fachat/csa_cbmio/petio/Shell.vhd

----------------------------------------------------------------------------------
-- Company: 
-- Engineer: 
-- 
-- Create Date:    22:18:53 01/30/2026 
-- Design Name: 
-- Module Name:    Shell - Behavioral 
-- Project Name: 
-- Target Devices: 
-- Tool versions: 
-- Description: 
--
-- Dependencies: 
--
-- Revision: 
-- Revision 0.01 - File Created
-- Additional Comments: 
--
----------------------------------------------------------------------------------
library IEEE;
use IEEE.STD_LOGIC_1164.ALL;
use IEEE.STD_LOGIC_unsigned.ALL;
use ieee.numeric_std.all;

-- Uncomment the following library declaration if using
-- arithmetic functions with Signed or Unsigned values
--use IEEE.NUMERIC_STD.ALL;

-- Uncomment the following library declaration if instantiating
-- any Xilinx primitives in this code.
library UNISIM;
use UNISIM.VComponents.all;

entity Shell is
	Port (
		phi2: in std_logic;
		rwb: in std_logic;
		niosel: in std_logic;
		nres: in std_logic;
		A: in std_logic_vector(11 downto 0);
		D: inout std_logic_vector(7 downto 0);
				
		irq: out std_logic;
		nbe: out std_logic;
		
		-- Test fixture toggle
		-- used in test bench only, so defaults to off
		test_enable: in std_logic := '0';
		
		-- SPI (5V)
		spiiosel: out std_logic;
		spimosi: out std_logic;
		spimiso: in std_logic;
		spiclk: out std_logic;
		
		-- "left" rs232
		lcts: in std_logic;
		lrts: out std_logic;
		lrx: in std_logic;
		ltx: out std_logic;
		ldsr: in std_logic;
		ldtr: out std_logic;
		ldcd: in std_logic;
		lri: in std_logic;
		
		-- "right" rs232
		rcts: in std_logic;
		rrts: out std_logic;
		rrx: in std_logic;
		rtx: out std_logic;
		rdsr: in std_logic;
		rdtr: out std_logic;
		--rdcd: in std_logic;
		--rri: in std_logic;
		
		-- cassette interface
		c1sw: inout std_logic;
		cwr: inout std_logic;
		c1rd: in std_logic;
		c1mtr: out std_logic;
		
		-- userport
		up: inout std_logic_vector(13 downto 0);
		
		-- serial IEC
		datain: in std_logic;
		clkin: in std_logic;
		satnin: in std_logic;
		srqin: in std_logic;
		dataout: out std_logic;
		clkout: out std_logic;
		satnout: out std_logic;
		srqout: out std_logic;
		
		-- keyboard
		ksel: out std_logic_vector(3 downto 0);
		kin: in std_logic_vector(7 downto 0);
		
		-- IEEE488
		dio: inout std_logic_vector(7 downto 0);
		ren: inout std_logic;
		ifc: inout std_logic;
		ndac: inout std_logic;
		nrfd: inout std_logic;
		dav: inout std_logic;
		eoi: inout std_logic;
		atn: inout std_logic;
		psrq: inout std_logic;
		te: out std_logic;
		dc: out std_logic
	);
end Shell;

architecture Behavioral of Shell is

	signal D_in: std_logic_vector(7 downto 0);
	signal D_out: std_logic_vector(7 downto 0);
		
	signal nbe_out: std_logic;
	signal res: std_logic;
	signal phi2_int: std_logic;
	signal phi2_clk: std_logic;
	signal phi2_ibuf: std_logic;
	
	signal int_out: std_logic;
	signal qclk: std_logic;
	signal qclk_locked: std_logic;
	signal clk200_raw: std_logic;
	signal clk200: std_logic;
	signal clk200_locked: std_logic;
	signal clk200_status: std_logic_vector(1 downto 0);
	signal phi2x8: std_logic;
	signal phi2falling_en: std_logic;
	signal phi2rising_en: std_logic;
	signal uart_nres: std_logic;

	-- IEEE488 signals output from PET (depends on direction)
	signal ieee_is_out: std_logic;	-- 1 when sending from host (us) to device (on bus)
	signal ndac_out: std_logic;
	signal nrfd_out: std_logic;
	signal dav_out: std_logic;
	signal atn_out: std_logic;
	signal srq_out: std_logic;
	signal eoi_out: std_logic;
	signal dio_out: std_logic_vector(7 downto 0);

	-- Serial IEC
	signal fserdir: std_logic;
	
	-- components and related signals
	
	component ioselect is
    Port ( A : in  STD_LOGIC_VECTOR (11 downto 0);
           niosel : in  STD_LOGIC;
			  iopage : in STD_LOGIC;
			  nres : in STD_LOGIC;
			  nbe : out std_logic;
           pia1 : out  STD_LOGIC;
           pia2 : out  STD_LOGIC;
           via1 : out  STD_LOGIC;
           via2 : out  STD_LOGIC;
           uart1 : out  STD_LOGIC;
           uart2 : out  STD_LOGIC);	
	end component;

	signal pia1_sel: std_logic;
	signal pia1_irq: std_logic;
	signal pia1_din: std_logic_vector(7 downto 0);
	signal pia1_dout: std_logic_vector(7 downto 0);
	signal pia1_pa_in: std_logic_vector(7 downto 0);
	signal pia1_pa_dir: std_logic_vector(7 downto 0);
	signal pia1_pa_out: std_logic_vector(7 downto 0);
	signal pia1_ca1_in: std_logic;
	signal pia1_ca2_in: std_logic;
	signal pia1_ca2_out: std_logic;
	signal pia1_pb_in: std_logic_vector(7 downto 0);
	signal pia1_pb_dir: std_logic_vector(7 downto 0);
	signal pia1_pb_out: std_logic_vector(7 downto 0);
	signal pia1_cb1_in: std_logic;
	signal pia1_cb2_in: std_logic;
	signal pia1_cb2_out: std_logic;

	signal pia2_sel: std_logic;
	signal pia2_irq: std_logic;
	signal pia2_din: std_logic_vector(7 downto 0);
	signal pia2_dout: std_logic_vector(7 downto 0);
	signal pia2_pa_in: std_logic_vector(7 downto 0);
	signal pia2_pa_dir: std_logic_vector(7 downto 0);
	signal pia2_pa_out: std_logic_vector(7 downto 0);
	signal pia2_ca1_in: std_logic;
	signal pia2_ca2_in: std_logic;
	signal pia2_ca2_out: std_logic;
	signal pia2_pb_in: std_logic_vector(7 downto 0);
	signal pia2_pb_dir: std_logic_vector(7 downto 0);
	signal pia2_pb_out: std_logic_vector(7 downto 0);
	signal pia2_cb1_in: std_logic;
	signal pia2_cb2_in: std_logic;
	signal pia2_cb2_out: std_logic;

	signal via1_sel: std_logic;
	signal via1_irq: std_logic;
	signal via1_wren: std_logic;
	signal via1_rden: std_logic;
	signal via1_din: std_logic_vector(7 downto 0);
	signal via1_dout: std_logic_vector(7 downto 0);
	signal via1_pa_in: std_logic_vector(7 downto 0);
	signal via1_pa_out: std_logic_vector(7 downto 0);
	signal via1_pa_dir: std_logic_vector(7 downto 0);
	signal via1_ca1_in: std_logic;
	signal via1_ca2_in: std_logic;
	signal via1_ca2_out: std_logic;
	signal via1_ca2_dir: std_logic;
	signal via1_pb_in: std_logic_vector(7 downto 0);
	signal via1_pb_out: std_logic_vector(7 downto 0);
	signal via1_pb_dir: std_logic_vector(7 downto 0);
	signal via1_cb1_in: std_logic;
	signal via1_cb1_out: std_logic;
	signal via1_cb1_dir: std_logic;
	signal via1_cb2_in: std_logic;
	signal via1_cb2_out: std_logic;
	signal via1_cb2_dir: std_logic;

	signal via2_sel: std_logic;
	signal via2_irq: std_logic;
	signal via2_wren: std_logic;
	signal via2_rden: std_logic;
	signal via2_din: std_logic_vector(7 downto 0);
	signal via2_dout: std_logic_vector(7 downto 0);
	signal via2_pa_in: std_logic_vector(7 downto 0);
	signal via2_pa_out: std_logic_vector(7 downto 0);
	signal via2_pa_dir: std_logic_vector(7 downto 0);
	signal via2_ca1_in: std_logic;
	signal via2_ca2_in: std_logic;
	signal via2_ca2_out: std_logic;
	signal via2_ca2_dir: std_logic;
	signal via2_pb_in: std_logic_vector(7 downto 0);
	signal via2_pb_out: std_logic_vector(7 downto 0);
	signal via2_pb_dir: std_logic_vector(7 downto 0);
	signal via2_cb1_in: std_logic;
	signal via2_cb1_out: std_logic;
	signal via2_cb1_dir: std_logic;
	signal via2_cb2_in: std_logic;
	signal via2_cb2_out: std_logic;
	signal via2_cb2_dir: std_logic;
	
	signal uart1_sel: std_logic;
	signal uart1_irq: std_logic;
	signal uart1_din: std_logic_vector(7 downto 0);
	signal uart1_dout: std_logic_vector(7 downto 0);

	signal uart2_sel: std_logic;
	signal uart2_irq: std_logic;
	signal uart2_din: std_logic_vector(7 downto 0);
	signal uart2_dout: std_logic_vector(7 downto 0);
	
	component pia6520 is
    Port ( nres : in  STD_LOGIC;
           phi2 : in  STD_LOGIC;
           rwb : in  STD_LOGIC;
           sel : in  STD_LOGIC;
           irq : out  STD_LOGIC;
			  addr : in STD_LOGIC_VECTOR(1 downto 0);
           data_in : in  STD_LOGIC_VECTOR (7 downto 0);
           data_out : out  STD_LOGIC_VECTOR (7 downto 0);

           porta_in : in  STD_LOGIC_VECTOR (7 downto 0);
           porta_dir : out  STD_LOGIC_VECTOR (7 downto 0);
           porta_out : out  STD_LOGIC_VECTOR (7 downto 0);
           ca1_in : in  STD_LOGIC;
           ca2_in : in  STD_LOGIC;
           ca2_out : out  STD_LOGIC;
			  
           portb_in : in  STD_LOGIC_VECTOR (7 downto 0);
           portb_dir : out  STD_LOGIC_VECTOR (7 downto 0);
           portb_out : out  STD_LOGIC_VECTOR (7 downto 0);
           cb1_in : in  STD_LOGIC;
           cb2_in : in  STD_LOGIC;
           cb2_out : out  STD_LOGIC);
	end component;

	component via6522 is
		port (
			phi2        : in  std_logic;
			phi2x8      : in  std_logic;
			phi2falling_en : in  std_logic;
			phi2rising_en  : in  std_logic;
			reset       : in  std_logic;
    
			addr        : in  std_logic_vector(3 downto 0);
			wen         : in  std_logic;
			ren         : in  std_logic;
			data_in     : in  std_logic_vector(7 downto 0);
			data_out    : out std_logic_vector(7 downto 0);

--			phi2_ref    : out std_logic;

			-- pio --
			port_a_o    : out std_logic_vector(7 downto 0);
			port_a_t    : out std_logic_vector(7 downto 0);
			port_a_i    : in  std_logic_vector(7 downto 0);
    
			port_b_o    : out std_logic_vector(7 downto 0);
			port_b_t    : out std_logic_vector(7 downto 0);
			port_b_i    : in  std_logic_vector(7 downto 0);

			-- handshake pins
			ca1_i       : in  std_logic;

			ca2_o       : out std_logic;
			ca2_i       : in  std_logic;
			ca2_t       : out std_logic;
    
			cb1_o       : out std_logic;
			cb1_i       : in  std_logic;
			cb1_t       : out std_logic;
    
			cb2_o       : out std_logic;
			cb2_i       : in  std_logic;
			cb2_t       : out std_logic;

			irq         : out std_logic );
	end component;
	
	component ieeedir is
    Port ( 
           phi2 : in  STD_LOGIC;
           nres : in  STD_LOGIC;
			  dio_in : in  STD_LOGIC_VECTOR (7 downto 0);
           atn_in : in  STD_LOGIC;
           dav_in : in  STD_LOGIC;
           nrfd_in : in  STD_LOGIC;
			  is_out : out STD_LOGIC
	 );
	end component;

	component uart_shell is
    Port ( phi2 : in  STD_LOGIC;
           qclk : in  STD_LOGIC;
           rwb : in  STD_LOGIC;
           nres : in  STD_LOGIC;
			  sel : in STD_LOGIC;
           addr : in  STD_LOGIC_VECTOR (2 downto 0);
           din : in  STD_LOGIC_VECTOR (7 downto 0);
           dout : out  STD_LOGIC_VECTOR (7 downto 0);
           irq : out  STD_LOGIC;
           rx : in  STD_LOGIC;
           tx : out  STD_LOGIC;
           cts : in  STD_LOGIC;
           rts : out  STD_LOGIC;
           dsr : in  STD_LOGIC;
           dtr : out  STD_LOGIC;
           ri : in  STD_LOGIC;
           dcd : in  STD_LOGIC);
	end component;

	component qclk_pll is
    Port ( phi2 : in  STD_LOGIC;
           nres : in  STD_LOGIC;
           qclk : out  STD_LOGIC;
           phi2x8 : out  STD_LOGIC;
           phi2falling_en : out  STD_LOGIC;
           phi2rising_en : out  STD_LOGIC;
           locked : out  STD_LOGIC);
	end component;
	
	-- test timer (50Hz)
	signal test_counter: std_logic_vector(15 downto 0);
	-- test
	signal ign_rtx: std_logic;
	signal ign_rrts: std_logic;
	
	-- which I/O page to use (either 8 or 9)
	signal iopage: std_logic;
	
	-- divider for qclk
	signal qclk_cnt: std_logic_vector(7 downto 0);
	signal qclk_div: std_logic;

	attribute keep : string;
	attribute keep of clk200 : signal is "true";
	
begin

	-- phi2 is a CLK signal
	-- phi2_int isn't
	phi2_ibufg: IBUFG
		port map (
			I => phi2,
			O => phi2_ibuf
		);
	phi2_bufg: BUFG
		port map (
			I => phi2_ibuf,
			O => phi2_clk
		);

	clk200_gen: DCM_CLKGEN
		generic map (
			CLKFXDV_DIVIDE => 2,
			CLKFX_DIVIDE => 1,
			CLKFX_MD_MAX => 0.0,
			CLKFX_MULTIPLY => 200,
			CLKIN_PERIOD => 1000.0,
			SPREAD_SPECTRUM => "NONE",
			STARTUP_WAIT => FALSE
		)
		port map (
			CLKFX => clk200_raw,
			CLKFX180 => open,
			CLKFXDV => open,
			LOCKED => clk200_locked,
			PROGDONE => open,
			STATUS => clk200_status,
			CLKIN => phi2_clk,
			FREEZEDCM => '0',
			PROGCLK => '0',
			PROGDATA => '0',
			PROGEN => '0',
			RST => not nres
		);

	clk200_bufg: BUFG
		port map (
			I => clk200_raw,
			O => clk200
		);
	
	phi2_int <= phi2_ibuf;
	
--	phi2_int <= phi2;
--	phi2_clk <= phi2;
	
	rtx <= '1' when via1_sel ='1' and A(3 downto 0) = X"6" else '0';
	rrts <= qclk_div; --nbe_out; --D_in(2);
	iopage <= rcts;
	
	qclk_div_p: process(qclk, qclk_cnt, nres)
	begin
		if (nres = '0') then
--			qclk_cnt <= (others => '0');
		elsif (falling_edge(qclk)) then
				qclk_div <= not(qclk_div);
		end if;
	end process;
	
	
	irq <= pia1_irq 
		or pia2_irq 
		or via1_irq 
		or uart1_irq
		or uart2_irq
		or int_out;
	
	res <= not(nres);
	uart_nres <= nres and qclk_locked;
	
	D_in <= D;
	D <= (others => 'Z') when rwb = '0'
			else D_out;	
	D_out <= pia1_dout when pia1_sel = '1'
			else pia2_dout when pia2_sel = '1'
			else via1_dout when via1_sel = '1'
			else via2_dout when via2_sel = '1'
			else uart1_dout when uart1_sel = '1'
			else uart2_dout when uart2_sel = '1'
			else "11101000";	-- open bus pattern $e8
			--else (others => 'X');

	-- I/O
	
	-- userport (inputs)
	up(8) <= 'Z';
	up(12) <= 'Z' when via1_cb1_dir = '0' else via1_cb1_out;
	up(13) <= 'Z';

	-- SPI (5V)
	spimosi <= '1';
	spiclk <= '1';
	spiiosel <= '1';
	
	-- IEEE488
	
	-- Using the 7516x interface chips
	-- https://www.ti.com/lit/ds/symlink/sn75161b.pdf?ts=1774340006842
	--
	-- 75161 direction control; 0 = controller
	-- ATN out, SRQ in, REN out, IFC out
	dc <= '0';
	-- 7516x talk enable; 0: DAV in, EOI in (ATN hi), NRFD out, NDAC out
	-- 						 PET receives = TALK from device
	-- 7516x talk enable; 1: DAV out, EOI out, NRFD in, NDAC in
	-- 						 PET sends data = ATN, device LISTENs
	te <= ieee_is_out;
	
	atn <= atn_out;
	ren <= '1';
	ifc <= '1';
	psrq <= 'Z';

	ndac <= ndac_out when ieee_is_out = '0' else 'Z';
	nrfd <= nrfd_out when ieee_is_out = '0' else 'Z';
	dav <= dav_out when ieee_is_out = '1' else 'Z';
	eoi <= eoi_out when ieee_is_out = '1' else 'Z';
	
	dio(7 downto 0) <= dio_out when ieee_is_out = '1' else (others => 'Z');
	
	----------------------------------------------------
	-- fake interrupt as long as pia int does not seem to work
	
	fake_int: block
		signal int_cnt: std_logic_vector(15 downto 0);
	begin
	  int_p: process(phi2_int, nres)
	  begin
		if  (falling_edge(phi2_int)) then
			if (nres = '0') then
				int_cnt <= (others => '0');
			elsif (int_cnt > 20000) then
				int_cnt <= (others => '0');
			else
				int_cnt <= int_cnt + 1;
			end if;
		end if;
		if (rising_edge(phi2_int)) then
			if (int_cnt < 100) then
				int_out <= '1';
			else
				int_out <= '0';
			end if;
		end if;
	  end process;
	end block fake_int;
	
	----------------------------------------------------

	qclk_c: qclk_pll
		port map (
			phi2 => phi2_clk,
			nres => nres,
			qclk => qclk,
			phi2x8 => phi2x8,
			phi2falling_en => phi2falling_en,
			phi2rising_en => phi2rising_en,
			locked => qclk_locked
		);

	----------------------------------------------------

	pia1_c: pia6520
	   Port map (
			nres,
         phi2_int,
         rwb,
         pia1_sel,
         pia1_irq,
			A(1 downto 0),
         pia1_din,
			pia1_dout,

			pia1_pa_in,
			pia1_pa_dir,
			pia1_pa_out,			
         pia1_ca1_in,
         pia1_ca2_in,
         pia1_ca2_out,

			pia1_pb_in,
			pia1_pb_dir,
			pia1_pb_out,			
         pia1_cb1_in,
         pia1_cb2_in,
         pia1_cb2_out
		);

	pia1_din <= D_in;
	
	ksel <= pia1_pa_out(3 downto 0);
	pia1_pb_in <= kin;
	
	pia1_pa_in(7) <= up(10) when test_enable = '0' or via1_cb1_dir = '0' else via1_cb1_out;
	up(10) <= pia1_pa_out(7) when pia1_pa_dir(7) = '1' else 'Z';
	
	pia1_pa_in(6) <= eoi;
	pia1_pa_in(5) <= '1';	-- cass#2 switch
	pia1_pa_in(4) <= c1sw;	-- cass#1 switch
	pia1_pa_in(3 downto 0) <= pia1_pa_out(3 downto 0);

	c1sw <= pia1_pa_out(4) when pia1_pa_dir(0) = '1' else 'Z';
	
	-- cass#1 read
	pia1_ca1_in <= c1rd when test_enable = '0' or via1_ca2_dir = '0' else via1_ca2_out;
	-- eoi out
	pia1_ca2_in <= 'X';
	eoi_out <= pia1_ca2_out;
	
	pia1_cb1_in <= up(13);	-- vdrive
	pia1_cb2_in <= '1';	-- c1mtr out
	c1mtr <= pia1_cb2_out;
	
	----------------------------------------------------

	pia2_c: pia6520
	   Port map (
			nres,
         phi2_int,
         rwb,
         pia2_sel,
         pia2_irq,
			A(1 downto 0),
         pia2_din,
			pia2_dout,

			pia2_pa_in,
			pia2_pa_dir,
			pia2_pa_out,			
         pia2_ca1_in,
         pia2_ca2_in,
         pia2_ca2_out,

			pia2_pb_in,
			pia2_pa_dir,
			pia2_pb_out,			
         pia2_cb1_in,
         pia2_cb2_in,
         pia2_cb2_out
		);

	pia2_din <= D_in;
	
	pia2_pa_in <= dio;		-- dio out
	pia2_pb_in <= dio;
	dio_out <= pia2_pb_out;

	pia2_ca1_in <= atn;
	pia2_ca2_in <= 'X';		-- ndac out
	ndac_out <= pia2_ca2_out;
	
	pia2_cb1_in <= psrq;
	
	pia2_cb2_in <= 'X';		-- dav out
	dav_out <= pia2_cb2_out;
		
	----------------------------------------------------

	via1_c: via6522
	   Port map (
         phi2_clk,
			phi2x8,
			phi2falling_en,
			phi2rising_en,
			res,
			A(3 downto 0),
			via1_wren,
			via1_rden,			
         via1_din,
			via1_dout,

			via1_pa_out,			
			via1_pa_dir,			
			via1_pa_in,

			via1_pb_out,			
			via1_pb_dir,
			via1_pb_in,
			
         via1_ca1_in,
			
         via1_ca2_out,
         via1_ca2_in,
         via1_ca2_dir,

         via1_cb1_out,
         via1_cb1_in,
         via1_cb1_dir,

         via1_cb2_out,
         via1_cb2_in,
         via1_cb2_dir,
			
			via1_irq
		);
		
	via1_wren <= '1' when via1_sel = '1' and rwb = '0' else '0';
	via1_rden <= '1' when via1_sel = '1' and rwb = '1' else '0';
	
	via1_din <= D_in;

	via1_pa_in(0) <= up(0) when test_enable = '0' or via1_pa_dir(1) = '0' else via1_pa_out(1);
	via1_pa_in(1) <= up(1) when test_enable = '0' or via1_pa_dir(0) = '0' else via1_pa_out(0);
	via1_pa_in(2) <= up(2) when test_enable = '0' or via1_pa_dir(3) = '0' else via1_pa_out(3);
	via1_pa_in(3) <= up(3) when test_enable = '0' or via1_pa_dir(2) = '0' else via1_pa_out(2);
	via1_pa_in(4) <= up(7) when test_enable = '0' or via1_pb_dir(3) = '0' else via1_pb_out(3);
	via1_pa_in(5) <= up(6) when test_enable = '0' or via1_pa_dir(6) = '0' else via1_pa_out(6);
	via1_pa_in(6) <= up(5) when test_enable = '0' or via1_pa_dir(5) = '0' else via1_pa_out(5);
	via1_pa_in(7) <= up(4);
	
	via1_pb_in(0) <= ndac and ndac_out;
	via1_pb_in(1) <= 'Z'; -- nrfd out
	via1_pb_in(2) <= 'Z'; -- atn out
	via1_pb_in(3) <= cwr when test_enable = '0' or via1_pa_dir(4) = '0' else via1_pa_out(4);
	via1_pb_in(4) <= 'Z'; -- C2 MTR out
	
	up(0) <= via1_pa_out(0) when via1_pa_dir(0) = '1' else 'Z';
	up(1) <= via1_pa_out(1) when via1_pa_dir(1) = '1' else 'Z';
	up(2) <= via1_pa_out(2) when via1_pa_dir(2) = '1' else 'Z';
	up(3) <= via1_pa_out(3) when via1_pa_dir(3) = '1' else 'Z';
	up(4) <= via1_pa_out(7) when via1_pa_dir(7) = '1' else 'Z';
	up(5) <= via1_pa_out(6) when via1_pa_dir(6) = '1' else 'Z';
	up(6) <= via1_pa_out(5) when via1_pa_dir(5) = '1' else 'Z';
	up(7) <= via1_pa_out(4) when via1_pa_dir(4) = '1' else 'Z';
	
	nrfd_out <= via1_pb_out(1);
	atn_out <= via1_pb_out(2);
	cwr <= via1_pb_out(3) when via1_pb_dir(3) = '1' else 'Z';
	
	-- c2mtr <= via_pb_out(4);
	via1_pb_in(5) <= up(13);	-- vdrive
	via1_pb_in(6) <= nrfd and nrfd_out;
	via1_pb_in(7) <= dav;
	
	-- graphic
	up(11) <= via1_ca2_out when via1_ca2_dir = '1' else 'Z';
	via1_ca2_in <= up(11);
	
	-- Userport CA1
	via1_ca1_in <= up(8);
	-- Cass#2 read
	via1_cb1_in <= up(12) when test_enable = '0' or pia1_pa_dir(7) = '0' else pia1_pa_out(7);
	
	-- shift register in/out
	up(9) <= via1_cb2_out when via1_cb2_dir = '1' else 'Z';
	via1_cb2_in <= up(9) when test_enable = '0' or via1_pa_dir(7) = '0' else via1_pa_out(7);
	
	----------------------------------------------------

	via2_c: via6522
	   Port map (
         phi2_clk,
			phi2x8,
			phi2falling_en,
			phi2rising_en,
			res,
			A(3 downto 0),
			via2_wren,
			via2_rden,			
         via2_din,
			via2_dout,

			via2_pa_out,			
			via2_pa_dir,			
			via2_pa_in,

			via2_pb_out,			
			via2_pb_dir,
			via2_pb_in,
			
         via2_ca1_in,
			
         via2_ca2_out,
         via2_ca2_in,
         via2_ca2_dir,

         via2_cb1_out,
         via2_cb1_in,
         via2_cb1_dir,

         via2_cb2_out,
         via2_cb2_in,
         via2_cb2_dir,
			
			via2_irq
		);
		
	via2_ca1_in <= '1';
	via2_ca2_in <= '1';
	
	via2_wren <= '1' when via2_sel = '1' and rwb = '0' else '0';
	via2_rden <= '1' when via2_sel = '1' and rwb = '1' else '0';
	
	via2_din <= D_in;
	
	-- serial IEC bus
	-- TODO: satna, fast bus
	satnout 	<= via2_pb_out(3);
	clkout 	<= via2_pb_out(4);
	
	dataout 	<= via2_pb_out(5) or not(via2_cb2_out) when fserdir = '0' 
				else via2_pb_out(5);	
--	srqout <= not(via2_cb1_out) when fserdir = '0' 
--				else '0';
	srqout <= '0';
	
	fserdir <= via2_pb_out(0);
	
	via2_cb1_in <= srqin or not(fserdir);
	via2_cb2_in <= datain or not(fserdir);
	
	via2_pa_in <= (others => '1');
	
	via2_pb_in(0) <= '1'; -- fserdir
	via2_pb_in(1) <= '1'; -- satna
	via2_pb_in(2) <= not(satnin);	
	via2_pb_in(3) <= via2_pb_out(3);	-- atnout
	via2_pb_in(4) <= via2_pb_out(4);	-- clkout
	via2_pb_in(5) <= via2_pb_out(5);	-- dataout
	via2_pb_in(6) <= not(clkin);
	via2_pb_in(7) <= not(datain);

	----------------------------------------------------
	
--	uart1: uart_shell 
--    Port map ( 
--				phi2_int,
--				qclk,
--				rwb,
--				uart_nres,
--				uart1_sel,
--				A(2 downto 0),
--				uart1_din,
--				uart1_dout,
--				uart1_irq,
--				lrx,
--				ltx,
--				lcts,
--				lrts,
--				ldsr,
--				ldtr,
--				lri,
--				ldcd
--	);

	uart1_din <= D_in;

--	uart2: uart_shell 
--    Port map ( 
--				phi2_int,
--				qclk,
--				rwb,
--				uart_nres,
--				uart2_sel,
--				A(2 downto 0),
--				uart2_din,
--				uart2_dout,
--				uart2_irq,
--				rrx,
--				ign_rtx,
--				rcts,
--				ign_rrts,
--				rdsr,
--				rdtr,
--				'0',
--				'0'
--	);

	ltx <= '1';
	ldtr <= '1';
	rdtr <= '1';
	lrts <= '1';

	uart2_din <= D_in;
	
	----------------------------------------------------

	ieeedir_c: ieeedir
	port map(
		phi2_int,
		nres,
		not(dio),
		atn,
		dav,
		nrfd,
		ieee_is_out
	);
	
	-- IO select
	select_c: ioselect
	port map(
		A,
		niosel,
		iopage,
		nres,
		nbe_out,
		pia1_sel,
		pia2_sel,
		via1_sel,
		via2_sel,
		uart1_sel,
		uart2_sel
	);
	
	nbe <= nbe_out;
	
end Behavioral;
