fachat/csa_cbmio/petio/via6522_tmr_b.vhd

-------------------------------------------------------------------------------
-- Title      : VIA 6522 Timer B
-------------------------------------------------------------------------------

library ieee;
use ieee.std_logic_1164.all;
use ieee.std_logic_arith.all;
use ieee.std_logic_unsigned.all;

entity via6522_tmr_b is
port (
    phi2           : in  std_logic;
    phi2x8         : in  std_logic;
    phi2falling_en : in  std_logic;
    phi2rising_en  : in  std_logic;
    reset          : in  std_logic;
    acr            : in  std_logic_vector(7 downto 0);
    port_b_i       : in  std_logic_vector(7 downto 0);
    write_t2c_h    : in  std_logic;
    last_data      : in  std_logic_vector(7 downto 0);
    timer_b_latch  : in  std_logic_vector(7 downto 0);
    timer_b_count  : out std_logic_vector(15 downto 0);
    timer_b_event  : out std_logic;
    timer_b_sr_tick: out std_logic);
end via6522_tmr_b;

architecture rtl of via6522_tmr_b is
    constant latch_reset_pattern : std_logic_vector(15 downto 0) := X"5550";

    alias shift_mode_control : std_logic_vector(2 downto 0) is acr(4 downto 2);

    signal t2_count        : std_logic_vector(15 downto 0);
    signal t2_count_next   : std_logic_vector(15 downto 0);
    signal t2_count_prev   : std_logic_vector(15 downto 0);
    signal t2l_latch       : std_logic_vector(7 downto 0);
    signal w_t2c_h         : std_logic;
    signal t2_pb6_reg      : std_logic;
    signal t2_pb6_fall     : std_logic;
    signal t2l_ufl_prev    : std_logic;
    signal t2l_ufl_reg     : std_logic;
    signal t2h_ufl         : std_logic;
    signal t2l_load        : std_logic;
	 signal t2_cin				: std_logic;
    signal t2_run          : std_logic;
    signal s_t2            : std_logic;
    signal s_t2_prev       : std_logic;
begin

    timer_b_event <= s_t2;
    timer_b_count <= t2_count;
    t2l_latch <= timer_b_latch;
    timer_b_sr_tick <= t2l_ufl_reg;

    t2l_load <= '1' when (t2l_ufl_prev = '1' and (shift_mode_control = "100" or shift_mode_control(1 downto 0) = "01")) or w_t2c_h = '1' else '0';
    --t2_count_next <= (t2_count_prev - 1) when t2_cin = '1' else t2_count_prev;

    process(phi2x8)
        variable t2_pb6_sampled : std_logic;
    begin

		-- t2_pb6_reg is falling
		--> t2_pb6_fall is rising
		--> t2_pb6_sampled is rising
		if (rising_edge(phi2)) then
			if (reset = '1') then
				t2_pb6_fall <= '0';
			else
            t2_pb6_sampled := To_X01(port_b_i(6));
            if (t2_pb6_reg = '1' and t2_pb6_sampled = '0') then
					t2_pb6_fall <= '1';
            else
               t2_pb6_fall <= '0';
				end if;
         end if;
		end if;

		-- t2_pb6_sampled is rising
		--> t2_pb6_reg is falling
		if (falling_edge(phi2)) then
			if (reset = '1') then
				t2_pb6_reg <= '1';
			else
				t2_pb6_reg <= t2_pb6_sampled;
			end if;
      end if;

		-- write_t2c_h is incoming, valid at falling
		--> w_t2c_h is falling
		if (falling_edge(phi2)) then
			if (reset = '1') then
            w_t2c_h <= '0';
			else
            w_t2c_h <= write_t2c_h;
			end if;
		end if;

		-- w_t2c_h is falling
		-- t2l_latch is falling
		-- last_data is incoming, valid between falling
		-- t2_counter_next is t2_counter_prev is falling
		-- t2l_load is w_t2c_h, t2l_ufl_prev is falling
		--> t2_count is rising
		--> t2h_ufl is rising
		--> t2l_ufl_reg is rising
		if (rising_edge(phi2)) then
			if (reset = '1') then
				t2_count <= latch_reset_pattern;
            t2h_ufl <= '0';
            t2l_ufl_reg <= '0';
			else
                if (t2l_load = '1') then
                    t2_count(7 downto 0) <= t2l_latch;
                else
                    t2_count(7 downto 0) <= t2_count_next(7 downto 0);
                end if;

                if (w_t2c_h = '1') then
                    t2_count(15 downto 8) <= last_data;
                else
                    t2_count(15 downto 8) <= t2_count_next(15 downto 8);
                end if;

                if (t2_count_prev = x"0000" and t2_cin = '1' and w_t2c_h = '0') then
                    t2h_ufl <= '1';
                else
                    t2h_ufl <= '0';
                end if;
					 
                if t2_count_prev(7 downto 0) = x"00" and t2_cin = '1' and t2l_load = '0' then
                    t2l_ufl_reg <= '1';
                else
                    t2l_ufl_reg <= '0';
					 end if;
			end if;
		end if;

		-- t2_count is rising
		-- t2l_ufl_reg is rising
		--> t2_cin is falling
		--> t2_count_prev is falling
		--> t2l_ufl_prev is falling
		if (falling_edge(phi2)) then
			if (reset = '1') then
				t2_cin <= '0';
				t2_count_prev <= latch_reset_pattern;
				t2l_ufl_prev <= '0';
--				t2l_load <= '0';
			else
            if (acr(5) = '0' or t2_pb6_fall = '1') then
                t2_cin <= '1';
					 t2_count_next <= t2_count - 1;
            else
                t2_cin <= '0';
					 t2_count_next <= t2_count;
            end if;

--				if (write_t2c_h = '1'
--						or (t2l_ufl_reg = '1' 
--							and (shift_mode_control = "100" or shift_mode_control(1 downto 0) = "01")
--						)
--					) then
--					t2l_load <= '1';
--				else
--					t2l_load <= '0';
--				end if;
				
            t2_count_prev <= t2_count;
            t2l_ufl_prev  <= t2l_ufl_reg;
			end if;
		end if;

		-- t2_run is rising
		-- t2h_ufl is rising
		--> s_t2 is falling
		if (falling_edge(phi2)) then
			if (reset = '1') then
				s_t2 <= '0';
			else
                if t2_run = '1' and t2h_ufl = '1' then
                    s_t2 <= '1';
                else
                    s_t2 <= '0';
                end if;
         end if;
		end if;

		-- s_t2 is falling
		--> s_t2_prev is rising
		if (rising_edge(phi2)) then
			if (reset = '1') then
                s_t2_prev <= '0';
			else
                s_t2_prev <= s_t2;
			end if;
		end if;
		
		-- w_t2c_h is falling
		-- s_t2 is falling
		--> t2_run is rising
		if (rising_edge(phi2)) then
			if (reset = '1') then
				t2_run <= '0';
			else
				-- w_t2c_h is set at falling edge, s_t2_prev is set at rising edge
				if w_t2c_h = '1' then
					t2_run <= '1';
--				elsif s_t2_prev = '1' then
				elsif s_t2 = '1' then
					t2_run <= '0';
				end if;
			end if;
		end if;

    end process;
end rtl;
